HynekBaran/Raspi-NRF24-header/photos/20160223_103340.jpg

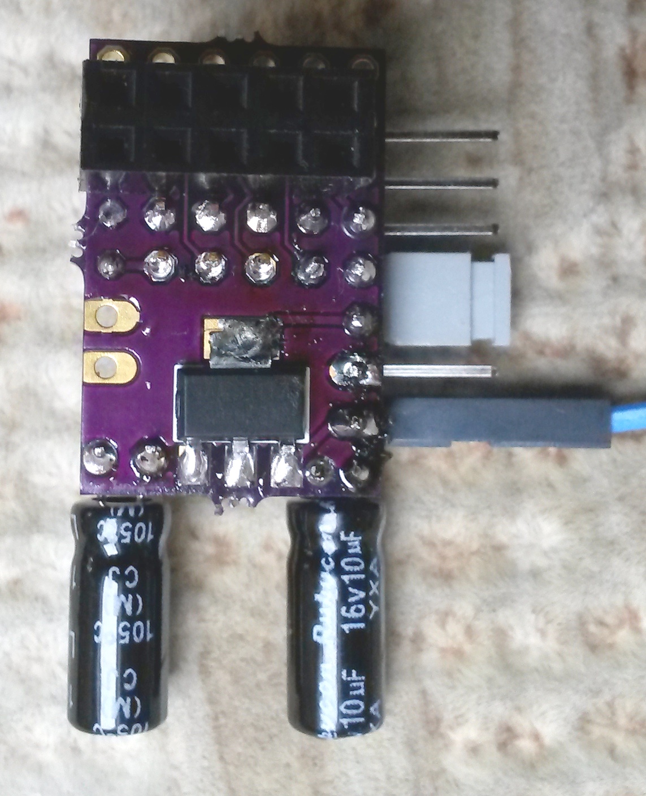
photos/20160223_103340.jpg
